cartheur/M6x09-II-SBC/images/acia-burst.jpg

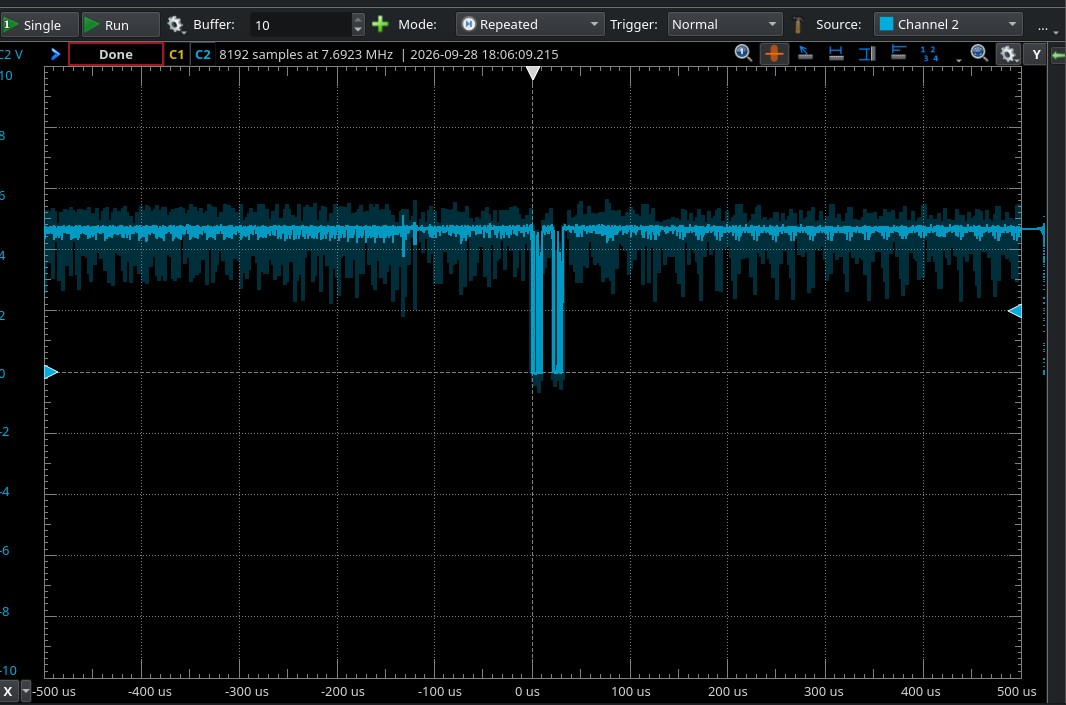
images/acia-burst.jpg
