cartheur/M6x09-II-SBC/images/acia-crystal-01.jpg

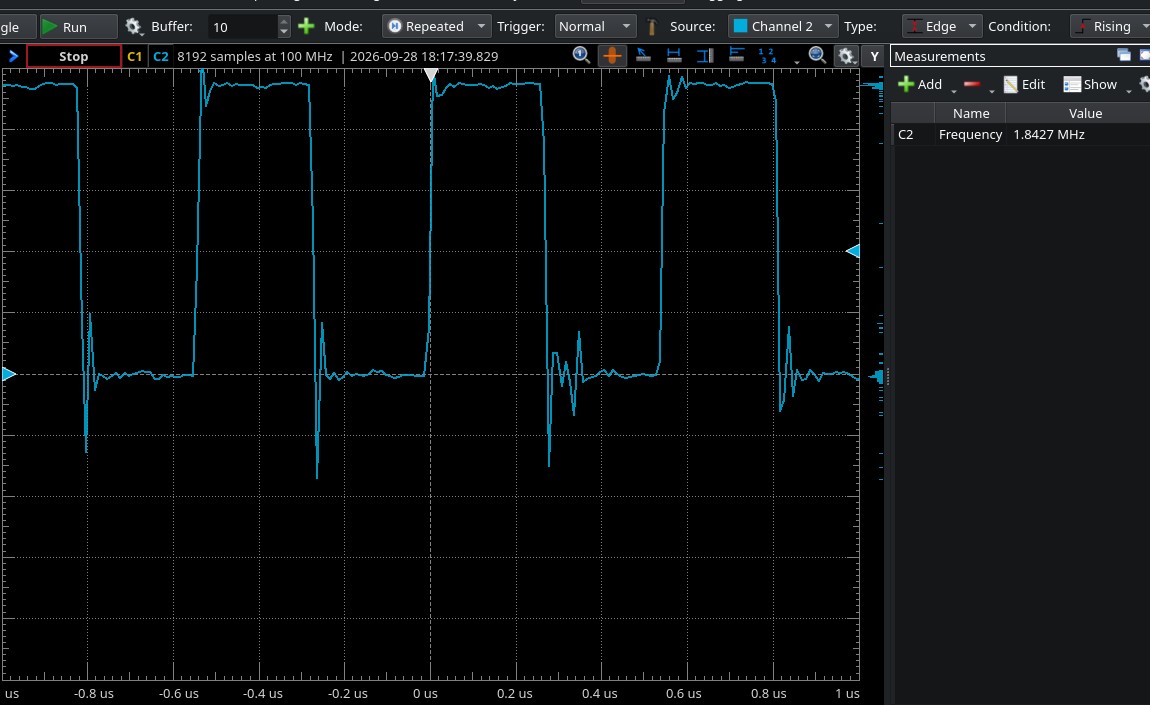
images/acia-crystal-01.jpg
