cartheur/M6x09-II-SBC/images/busses.jpg

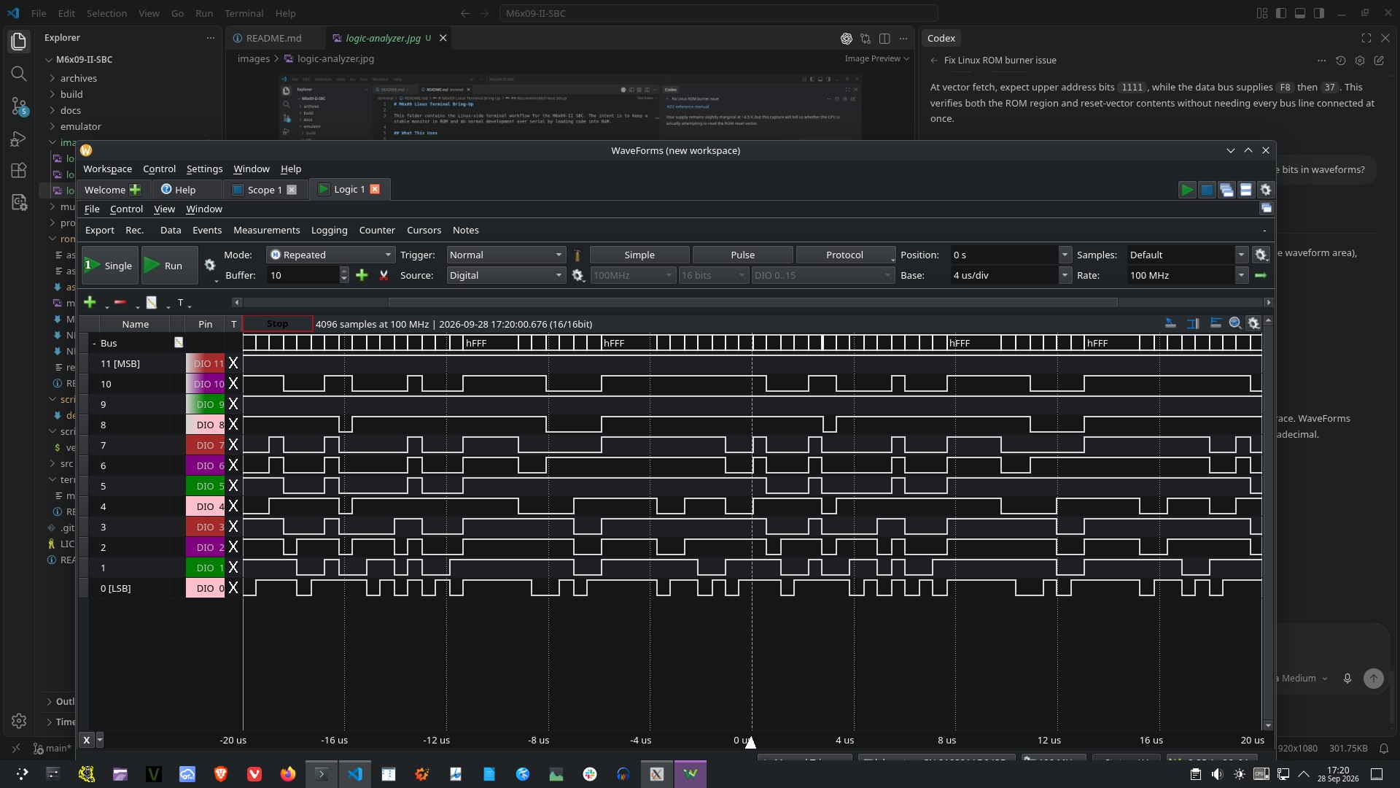
images/busses.jpg
