cartheur/M6x09-II-SBC/images/ch2-trigger-02.jpg

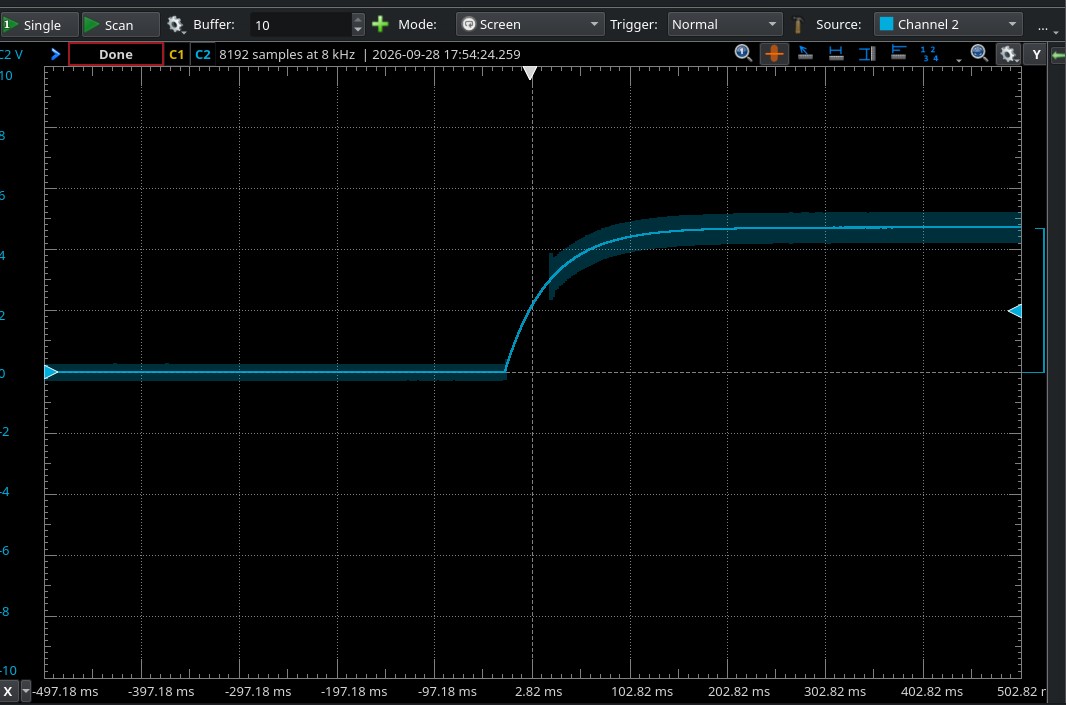
images/ch2-trigger-02.jpg
