cartheur/M6x09-II-SBC/images/ch2-trigger.jpg

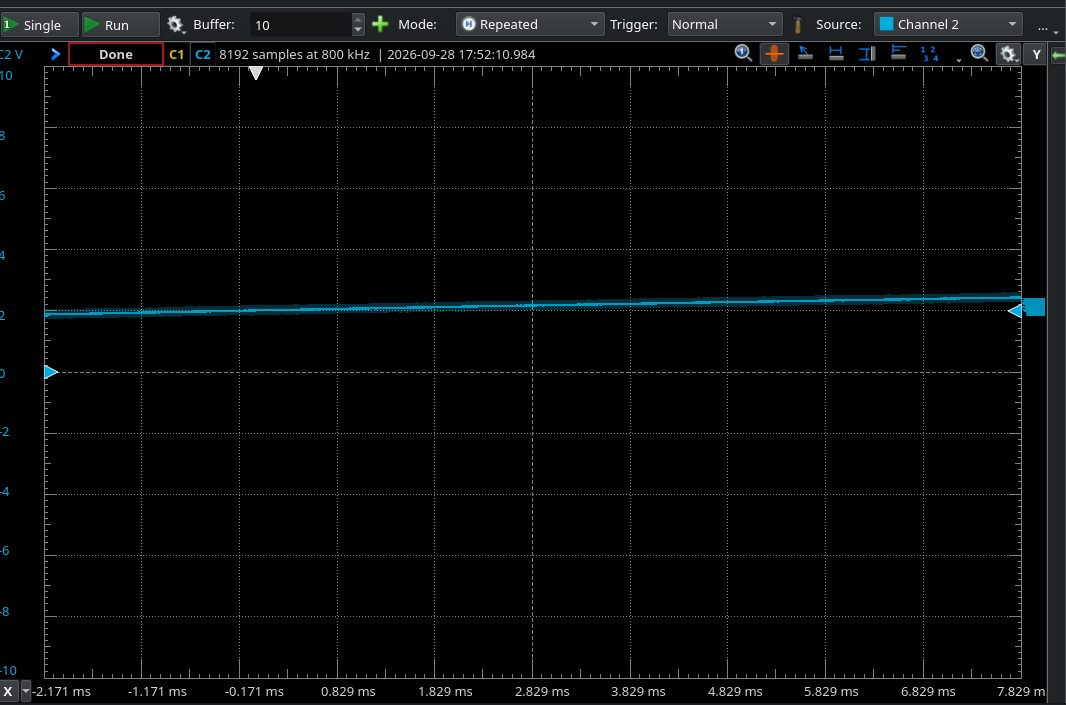
images/ch2-trigger.jpg
