cartheur/M6x09-II-SBC/images/first-acia.jpg

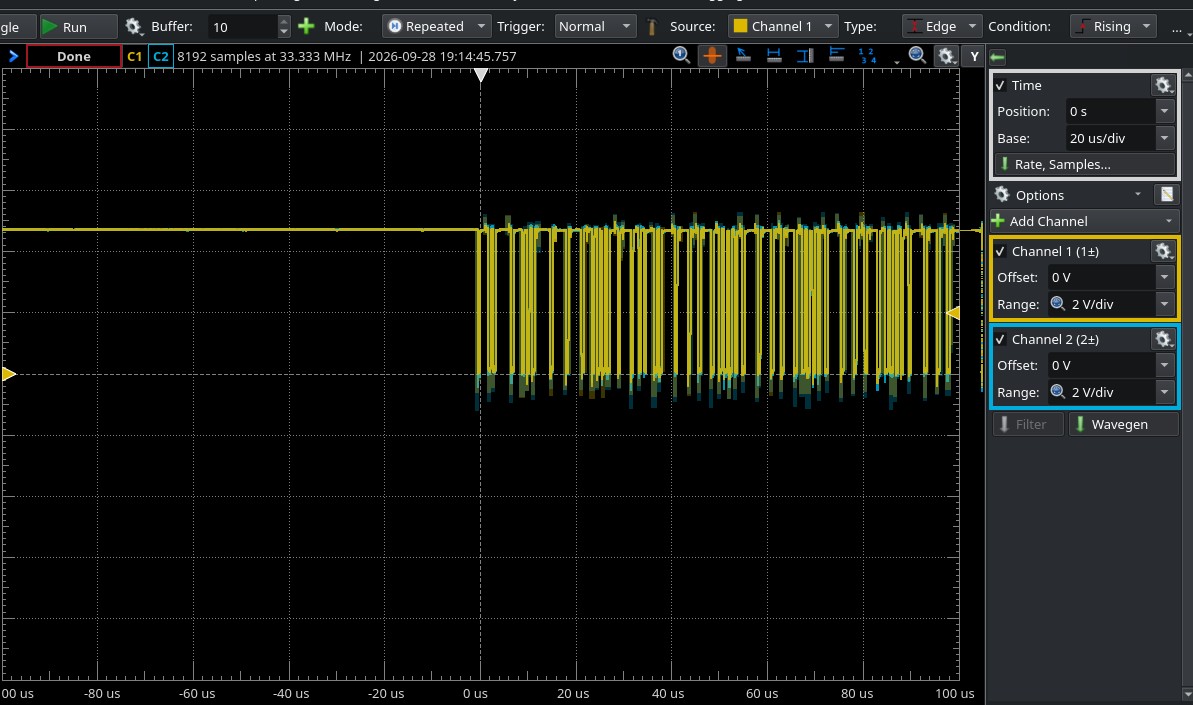
images/first-acia.jpg
