cartheur/M6x09-II-SBC/images/logic-analyzer-reset.jpg

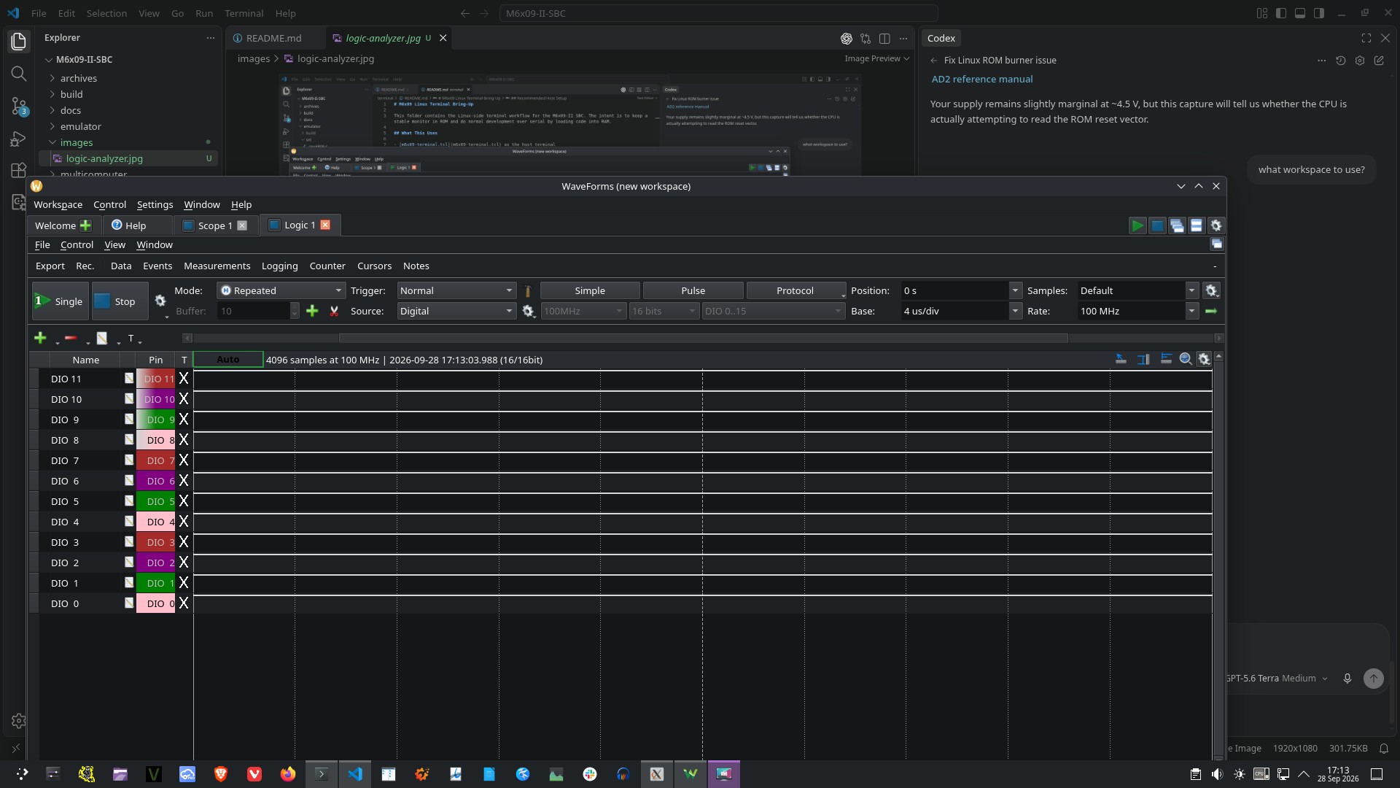
images/logic-analyzer-reset.jpg
