cartheur/M6x09-II-SBC/images/logic-analyzer-run.jpg

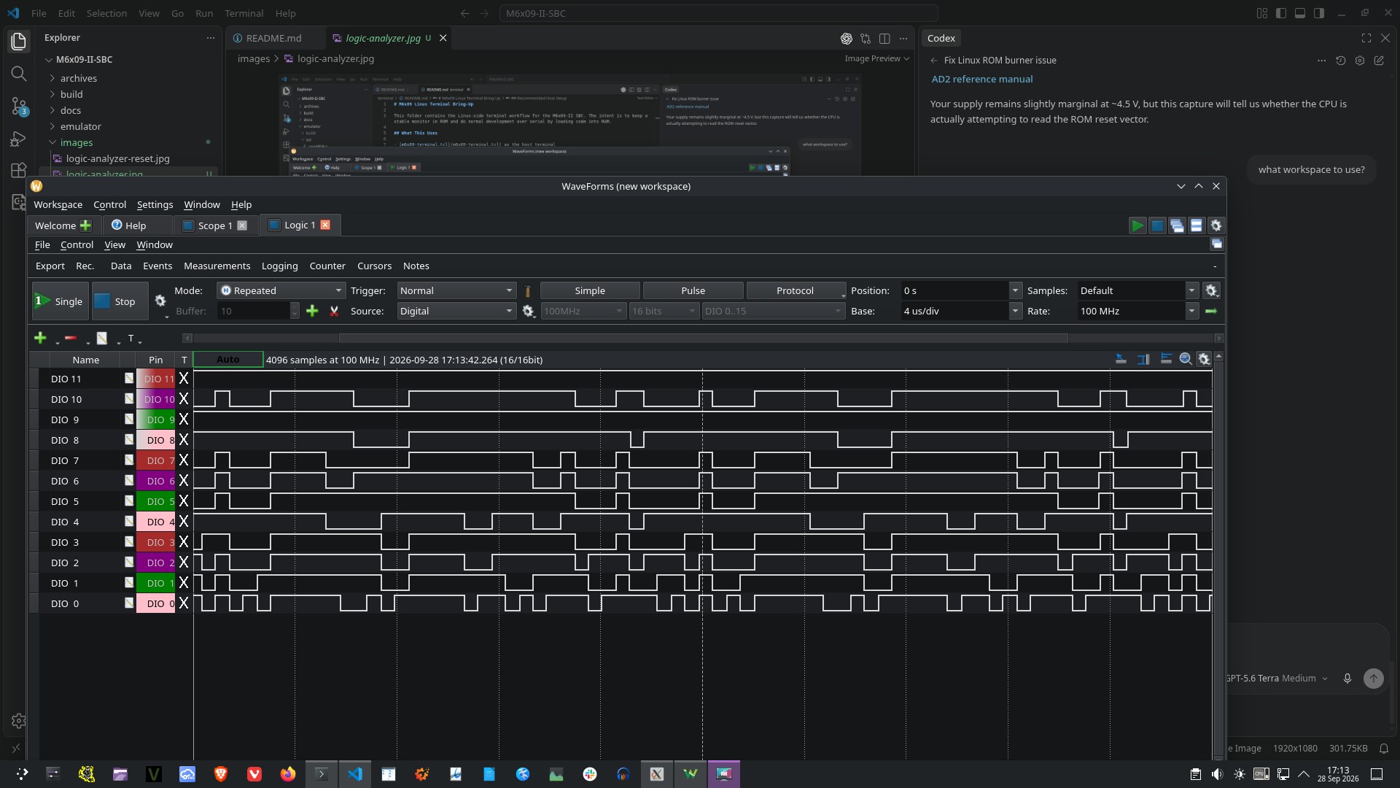
images/logic-analyzer-run.jpg
