cartheur/M6x09-II-SBC/images/logic-analyzer.jpg

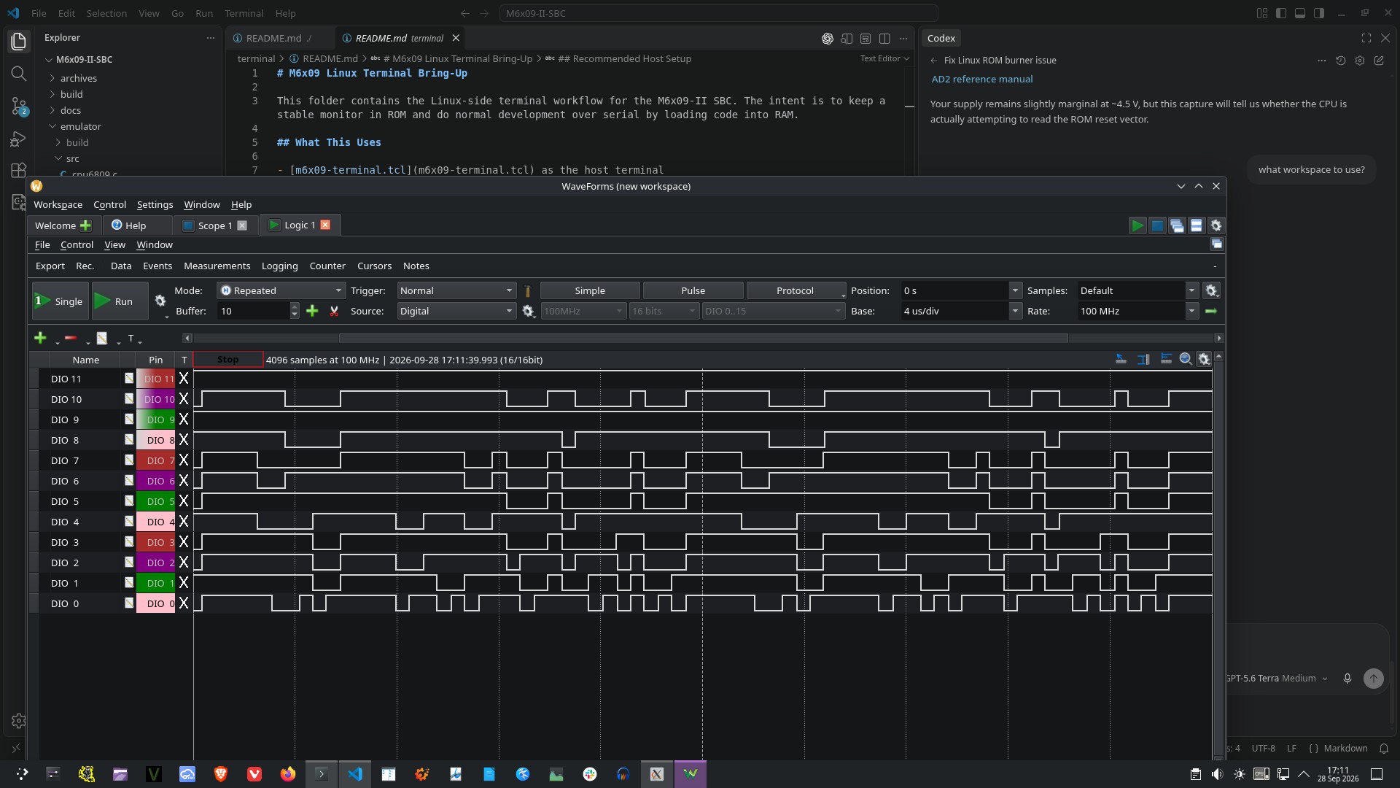
images/logic-analyzer.jpg
