cartheur/M6x09-II-SBC/images/RS.jpg

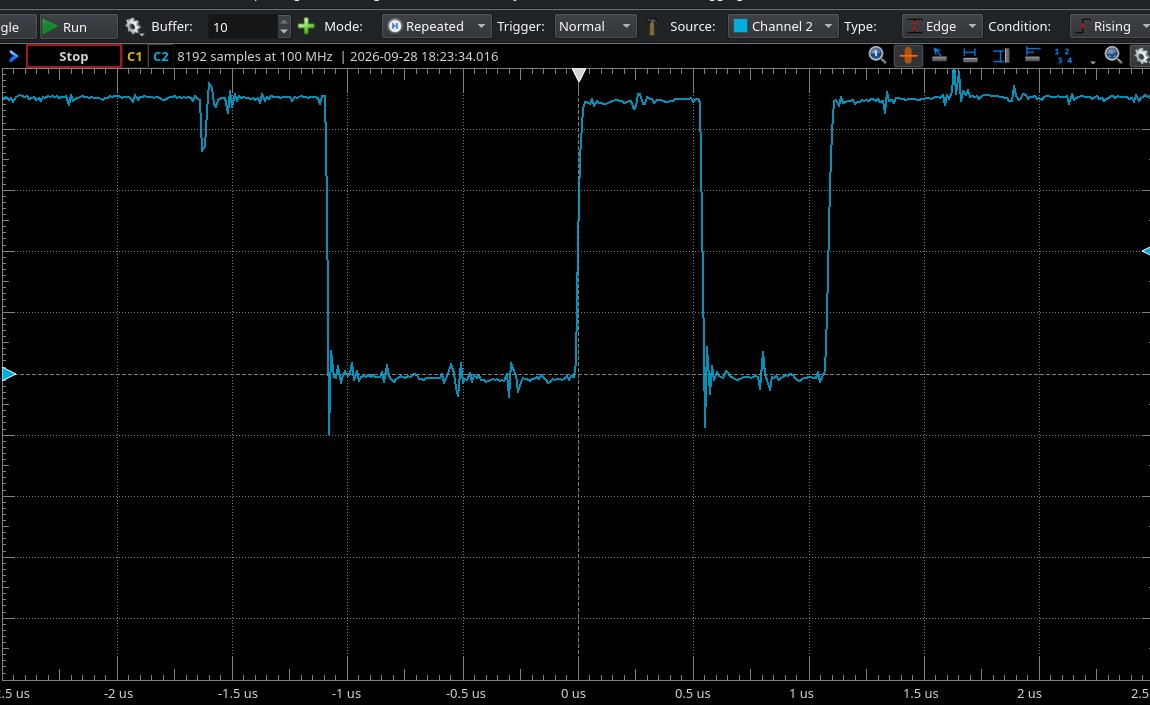
images/RS.jpg
