cartheur/M6x09-II-SBC/images/same-acia.jpg

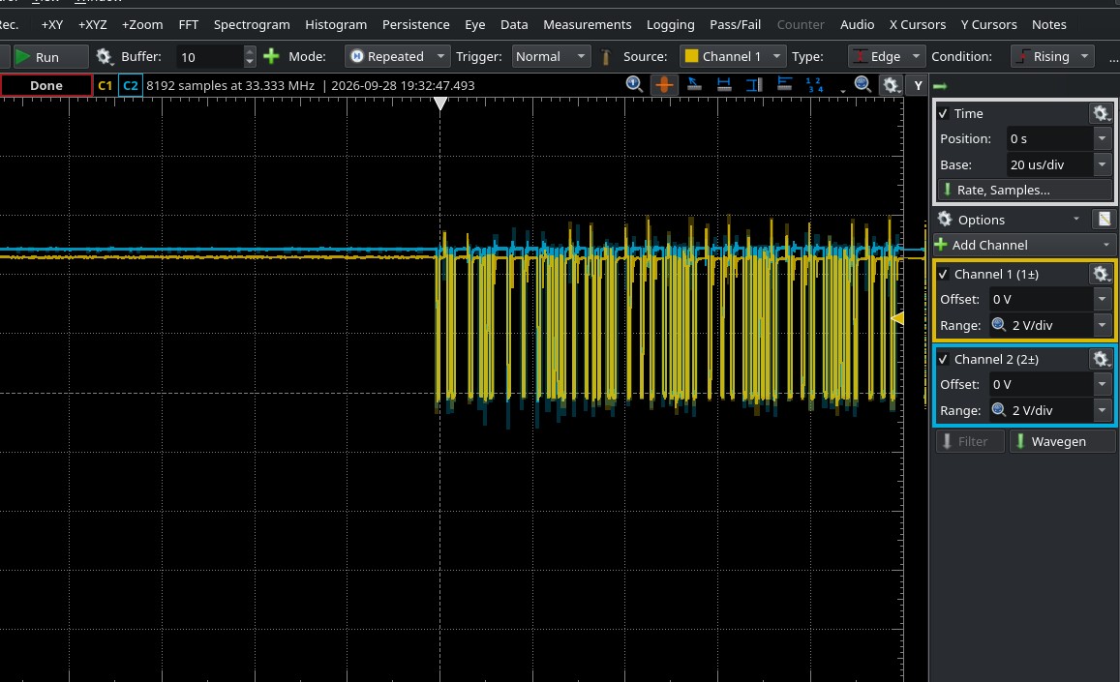
images/same-acia.jpg
