cartheur/M6x09-II-SBC/images/second-acia.jpg

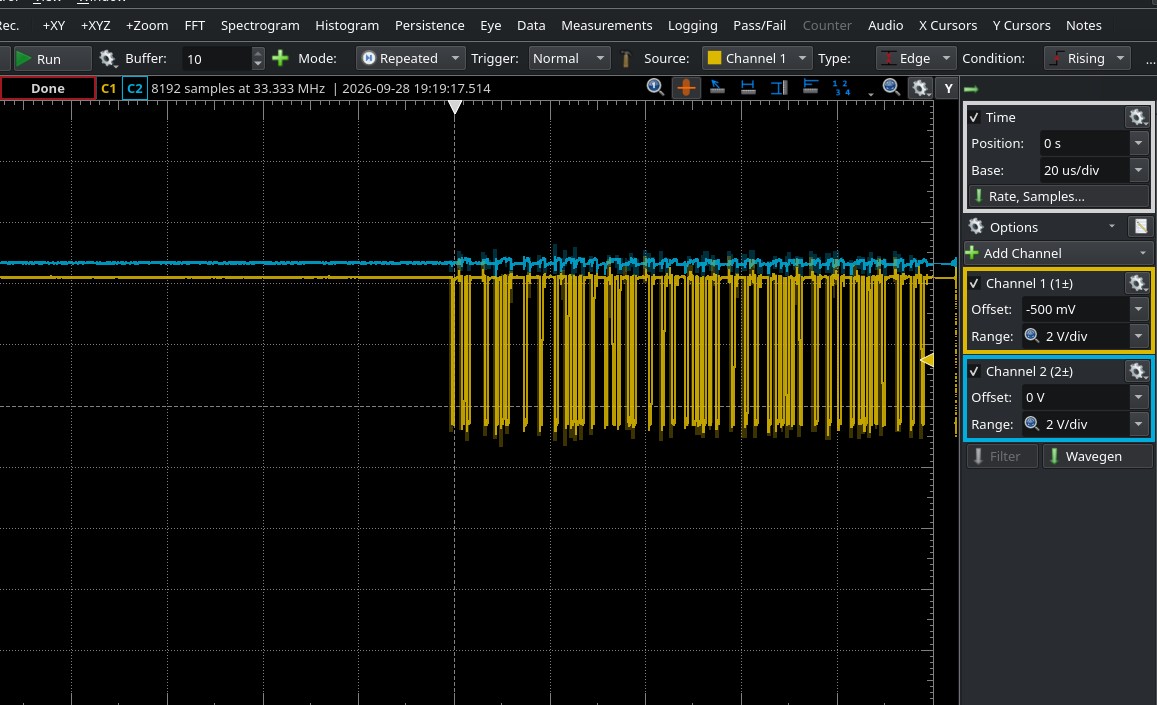
images/second-acia.jpg
