cartheur/M6x09-II-SBC/images/split-acia.jpg

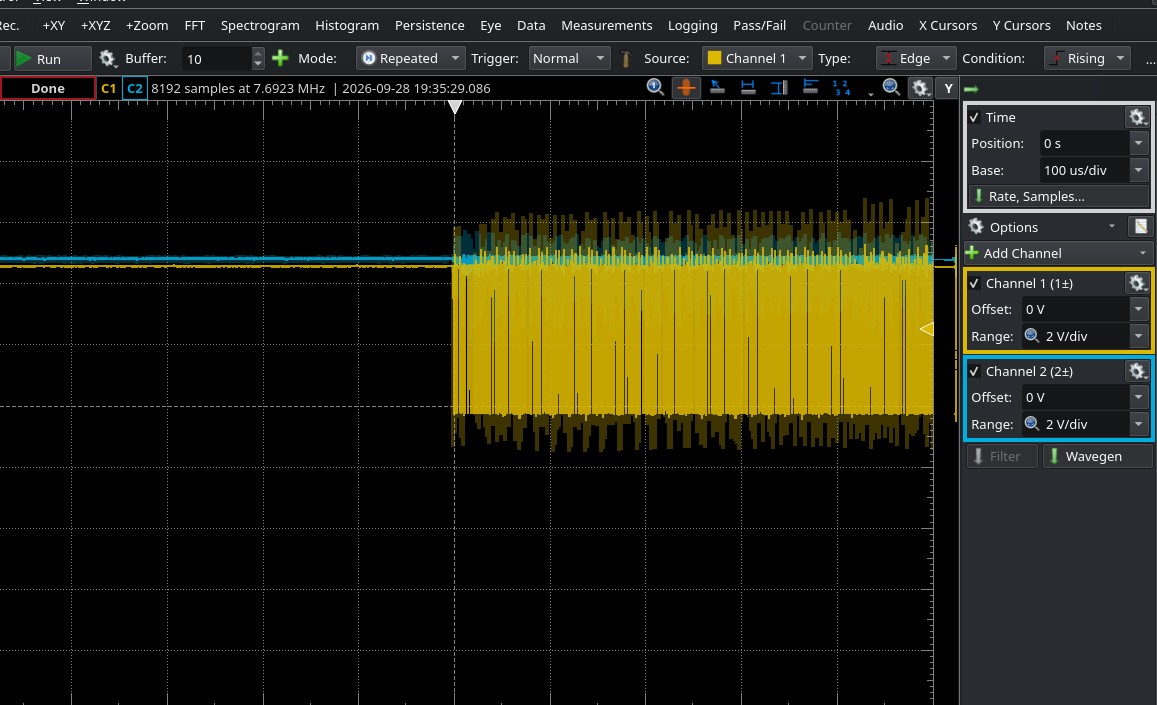
images/split-acia.jpg
