cartheur/M6x09-II-SBC/roms/memory-map.jpg

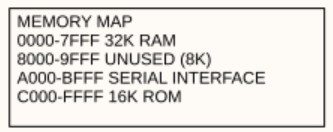
roms/memory-map.jpg
