cartheur/M6x09-II-SBC/build/alpha-board.jpg

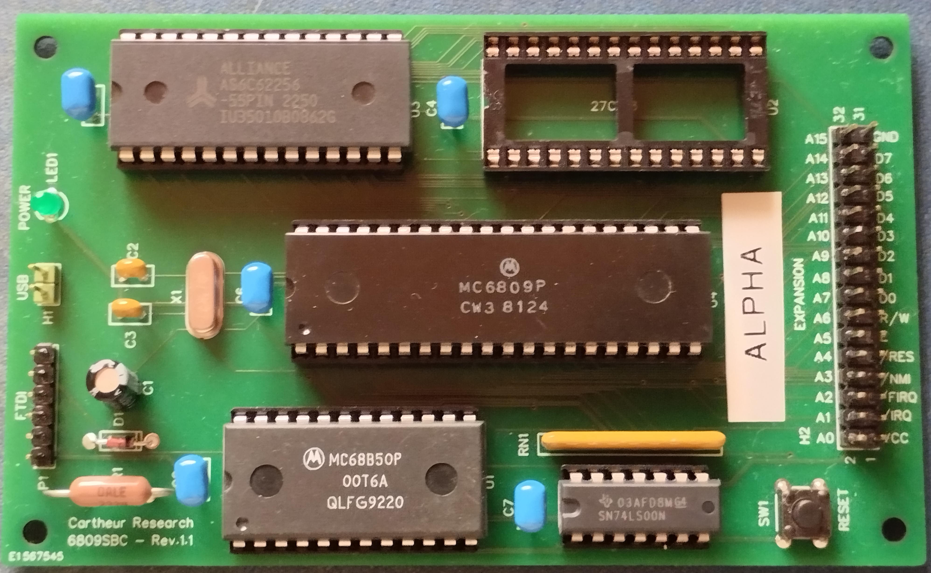
build/alpha-board.jpg
