cartheur/M6x09-II-SBC/build/gamma-board.jpg

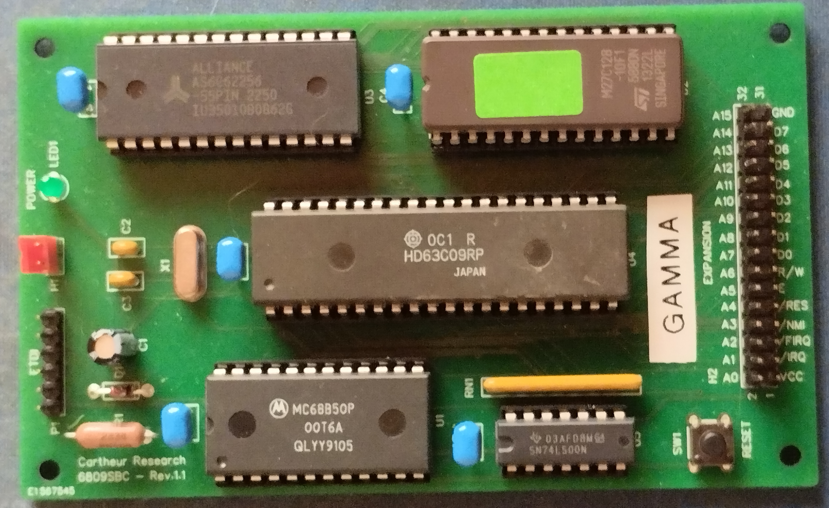
build/gamma-board.jpg
